TeXitoi/rusty-clock/images/10-power-led-resistor.jpg

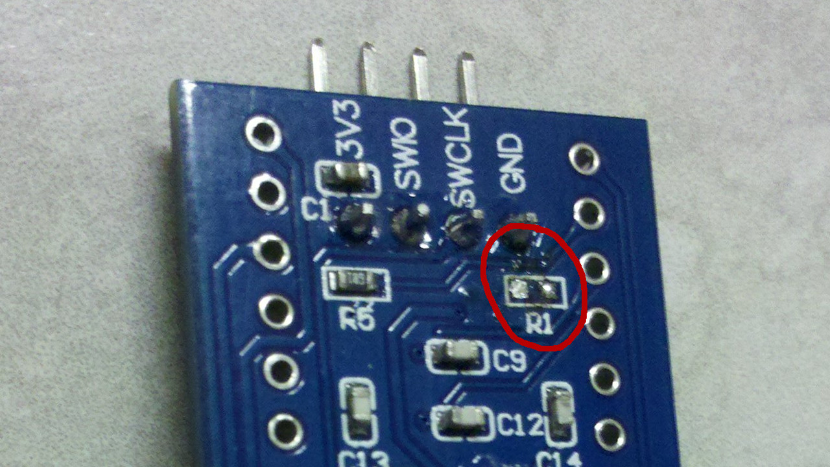
images/10-power-led-resistor.jpg
