TeXitoi/rusty-clock/images/11-blue-pill-headers.jpg

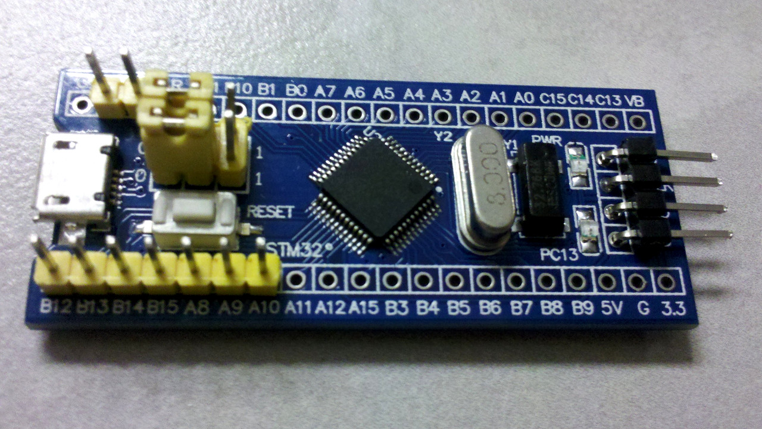
images/11-blue-pill-headers.jpg
