TeXitoi/rusty-clock/images/13-box-and-back.jpg

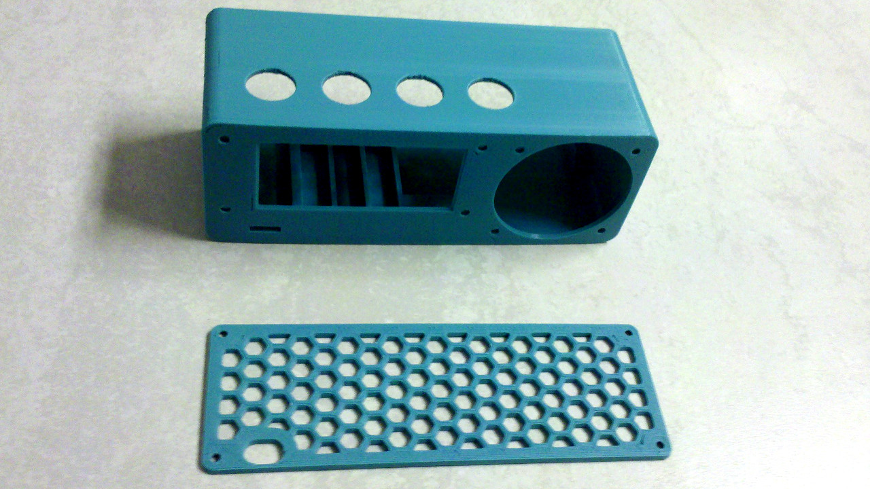
images/13-box-and-back.jpg
