TeXitoi/rusty-clock/images/19-ground-button-wire.jpg

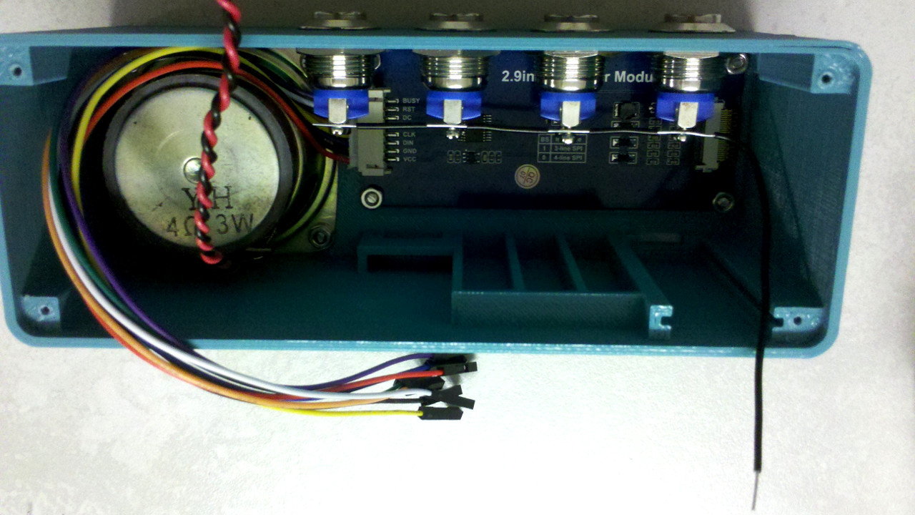
images/19-ground-button-wire.jpg
