TeXitoi/rusty-clock/images/20-wires.jpg

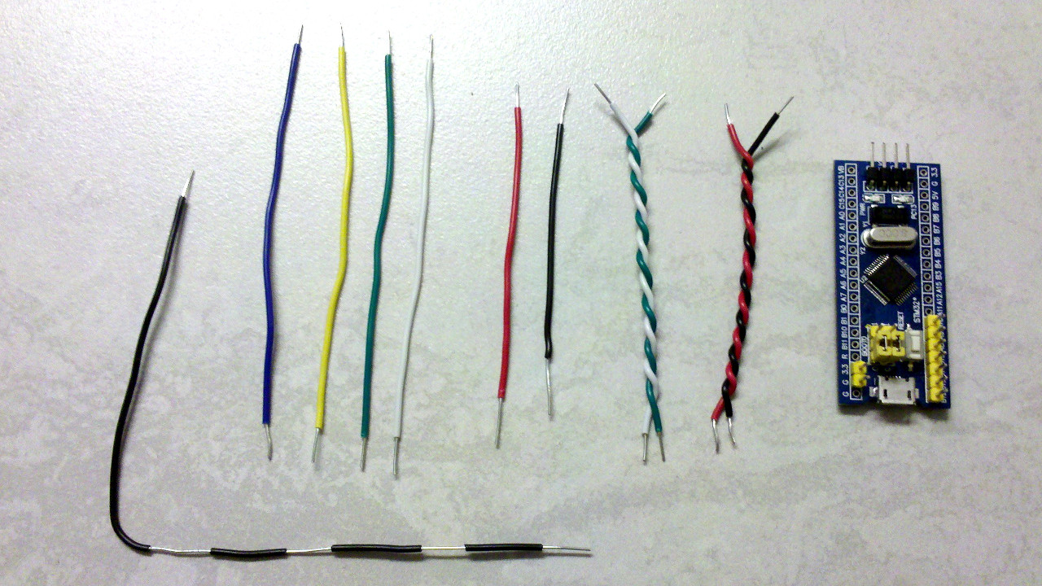
images/20-wires.jpg
