TeXitoi/rusty-clock/cad/box-v2/box-printing.scad

use <box.scad>
include <printing.scad>

box();
