TeXitoi/rusty-clock/images/15-fix-speaker-back.jpg

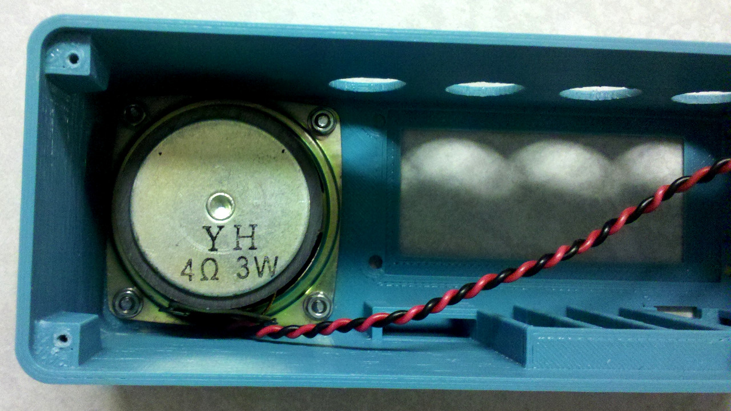
images/15-fix-speaker-back.jpg
