TeXitoi/rusty-clock/images/16-fix-display-front.jpg

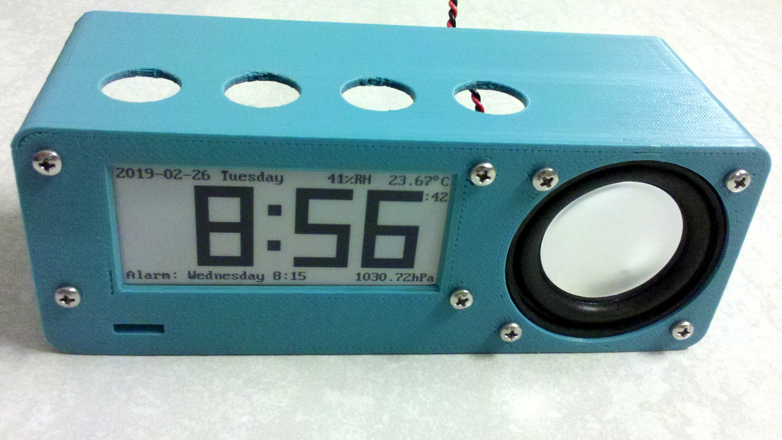
images/16-fix-display-front.jpg
