TeXitoi/rusty-clock/images/18-fix-buttons.jpg

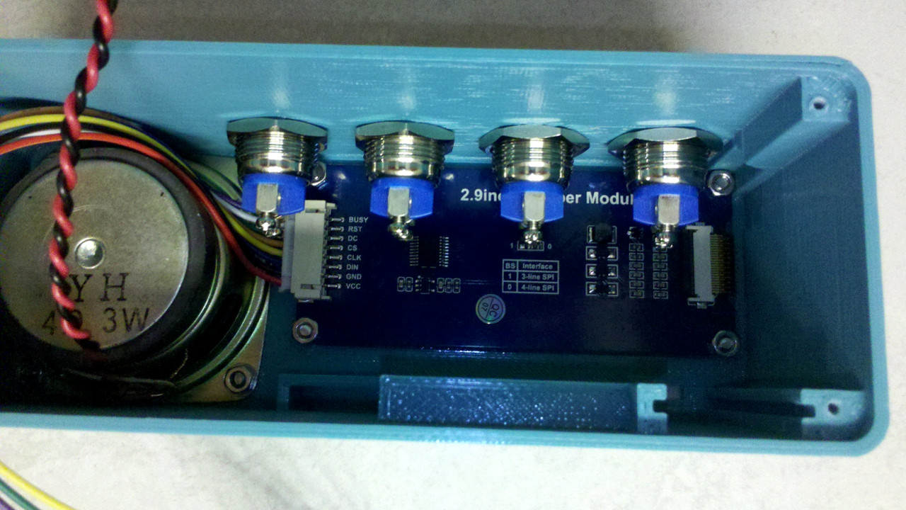
images/18-fix-buttons.jpg
