TeXitoi/rusty-clock/src/ui.rs

use core::convert::TryFrom;
use core::fmt::{self, Write};
use embedded_graphics::coord::Coord;
use embedded_graphics::fonts::{Font6x8, Font8x16};
use embedded_graphics::prelude::*;
use embedded_graphics::primitives::Rect;
use embedded_hal::blocking::i2c::WriteRead;
use heapless::{consts::*, String, Vec};
use il3820::DisplayRibbonLeft;
use rtc::datetime;

pub enum Msg {
    DateTime(datetime::DateTime),
    Environment(::bme280::Measurements<<::I2C as WriteRead>::Error>),
    ButtonMinus,
    ButtonOk,
    ButtonPlus,
}

pub enum Cmd {
    UpdateRtc(datetime::DateTime),
}

#[derive(Clone)]
pub struct Model {
    now: datetime::DateTime,
    /// unit: Pa
    pressure: u32,
    /// unit: c°C
    temperature: i16,
    /// unit: %
    humidity: u8,
    screen: Screen,
}

impl Model {
    pub fn init() -> Self {
        Self {
            now: datetime::DateTime::new(0),
            pressure: 0,
            temperature: 0,
            humidity: 0,
            screen: Screen::Clock,
        }
    }
    pub fn update(&mut self, msg: Msg) -> Vec<Cmd, U4> {
        use self::Screen::*;
        let mut cmds = Vec::new();

        match msg {
            Msg::DateTime(datetime) => self.now = datetime,
            Msg::Environment(measurements) => {
                self.pressure = measurements.pressure as u32;
                self.temperature = (measurements.temperature * 100.) as i16;
                self.humidity = measurements.humidity as u8;
            }
            Msg::ButtonOk => {
                self.screen = match ::core::mem::replace(&mut self.screen, Clock) {
                    Clock => Menu(MenuElt::Clock),
                    Menu(MenuElt::Clock) => Clock,
                    Menu(MenuElt::SetClock) => {
                        let mut dt = self.now.clone();
                        dt.sec = 0;
                        SetClock(EditDateTime::new(dt))
                    }
                    SetClock(mut edit) => if let Some(dt) = edit.ok() {
                        if let Err(_) = cmds.push(Cmd::UpdateRtc(dt)) {
                            panic!("cmds too small");
                        }
                        Clock
                    } else {
                        SetClock(edit)
                    },
                }
            }
            Msg::ButtonPlus => match &mut self.screen {
                Menu(elt) => *elt = elt.next(),
                SetClock(edit) => edit.next(),
                _ => {}
            },
            Msg::ButtonMinus => match &mut self.screen {
                Menu(elt) => *elt = elt.prev(),
                SetClock(edit) => edit.prev(),
                _ => {}
            },
        }
        cmds
    }
    pub fn view(&self) -> DisplayRibbonLeft {
        let mut display = DisplayRibbonLeft::default();

        self.render_header(&mut display);

        use self::Screen::*;
        match &self.screen {
            Clock => self.render_clock(&mut display),
            Menu(elt) => self.render_menu(elt, &mut display),
            SetClock(datetime) => self.render_set_clock(datetime, &mut display),
        }

        display
    }
    fn render_header(&self, display: &mut DisplayRibbonLeft) {
        let mut print = move |s: &str, x, y| {
            display.draw(
                Font6x8::render_str(s)
                    .with_stroke(Some(1u8.into()))
                    .translate(Coord::new(x, y))
                    .into_iter(),
            )
        };
        let mut s: String<U128> = String::new();
        write!(
            s,
            "{:4}-{:02}-{:02} {}",
            self.now.year, self.now.month, self.now.day, self.now.day_of_week,
        ).unwrap();
        print(&s, 4, 4);

        s.clear();
        write!(
            s,
            "{}{}C",
            Centi(self.temperature as i32),
            char::try_from('°' as u32 - 34).unwrap(),
        ).unwrap();
        print(&s, 4, 127 - 10);

        s.clear();
        write!(s, "{}hPa", Centi(self.pressure as i32),).unwrap();
        print(&s, 295 - 4 - 10 * 6, 127 - 10);

        if self.humidity != 0 {
            s.clear();
            write!(s, "{:2}%RH", self.humidity).unwrap();
            print(&s, 296 / 2 - 5 * 3, 127 - 10);
        }
    }
    fn render_clock(&self, display: &mut DisplayRibbonLeft) {
        let margin = 10;
        let digit = 50;
        let space = 12;

        if self.now.hour >= 10 {
            seven_segments(self.now.hour / 10, margin, 18, display);
        }
        seven_segments(self.now.hour % 10, margin + digit + space, 18, display);

        display.draw(
            Rect::new(
                Coord::new(margin + 2 * digit + 2 * space, 18 + 20),
                Coord::new(margin + 2 * digit + 2 * space + 9, 18 + 29),
            ).with_fill(Some(1u8.into()))
            .into_iter(),
        );
        display.draw(
            Rect::new(
                Coord::new(margin + 2 * digit + 2 * space, 18 + 60),
                Coord::new(margin + 2 * digit + 2 * space + 9, 18 + 69),
            ).with_fill(Some(1u8.into()))
            .into_iter(),
        );

        seven_segments(
            self.now.min / 10,
            margin + 2 * digit + 3 * space + 10,
            18,
            display,
        );
        seven_segments(
            self.now.min % 10,
            margin + 3 * digit + 4 * space + 10,
            18,
            display,
        );

        let mut s: String<U4> = String::new();
        write!(s, ":{:02}", self.now.sec).unwrap();
        display.draw(
            Font6x8::render_str(&s)
                .with_stroke(Some(1u8.into()))
                .translate(Coord::new(273, 18))
                .into_iter(),
        );
    }
    fn render_menu(&self, elt: &MenuElt, display: &mut DisplayRibbonLeft) {
        let mut s: String<U128> = String::new();
        write!(s, "Menu: {}", elt).unwrap();
        display.draw(
            Font8x16::render_str(&s)
                .with_stroke(Some(1u8.into()))
                .translate(Coord::new(12, 44))
                .into_iter(),
        );
    }
    fn render_set_clock(&self, datetime: &EditDateTime, display: &mut DisplayRibbonLeft) {
        let mut s: String<U128> = String::new();
        write!(s, "Set clock: {}", datetime).unwrap();
        display.draw(
            Font8x16::render_str(&s)
                .with_stroke(Some(1u8.into()))
                .translate(Coord::new(12, 44))
                .into_iter(),
        );
    }
}

struct Centi(i32);
impl fmt::Display for Centi {
    fn fmt(&self, f: &mut fmt::Formatter) -> fmt::Result {
        write!(f, "{}.{:02}", self.0 / 100, self.0 % 100)
    }
}

#[derive(Clone)]
enum Screen {
    Clock,
    Menu(MenuElt),
    SetClock(EditDateTime),
}
#[derive(Clone)]
enum MenuElt {
    Clock,
    SetClock,
}
impl MenuElt {
    fn next(&self) -> MenuElt {
        use self::MenuElt::*;
        match *self {
            Clock => SetClock,
            SetClock => Clock,
        }
    }
    fn prev(&self) -> MenuElt {
        use self::MenuElt::*;
        match *self {
            Clock => SetClock,
            SetClock => Clock,
        }
    }
}
impl fmt::Display for MenuElt {
    fn fmt(&self, f: &mut fmt::Formatter) -> fmt::Result {
        match self {
            MenuElt::Clock => f.write_str("clock"),
            MenuElt::SetClock => f.write_str("set clock"),
        }
    }
}
#[derive(Clone)]
struct EditDateTime {
    datetime: datetime::DateTime,
    state: EditDateTimeState,
}
#[derive(Clone)]
enum EditDateTimeState {
    Year,
    Month,
    Day,
    Hour,
    Min,
}
impl EditDateTime {
    fn new(datetime: datetime::DateTime) -> Self {
        Self {
            datetime,
            state: EditDateTimeState::Year,
        }
    }
    fn next(&mut self) {
        use self::EditDateTimeState::*;
        match self.state {
            Year => {
                self.datetime.year += 1;
                if self.datetime.year > 2105 {
                    self.datetime.year = 1970;
                }
            }
            Month => self.datetime.month = self.datetime.month % 12 + 1,
            Day => self.datetime.day = self.datetime.day % 31 + 1,
            Hour => self.datetime.hour = (self.datetime.hour + 1) % 24,
            Min => self.datetime.min = (self.datetime.min + 1) % 60,
        }
    }
    fn prev(&mut self) {
        use self::EditDateTimeState::*;
        match self.state {
            Year => {
                self.datetime.year -= 1;
                if self.datetime.year < 1970 {
                    self.datetime.year = 2105;
                }
            }
            Month => self.datetime.month = (self.datetime.month + 12 - 2) % 12 + 1,
            Day => self.datetime.day = (self.datetime.day + 31 - 2) % 31 + 1,
            Hour => self.datetime.hour = (self.datetime.hour + 24 - 1) % 24,
            Min => self.datetime.min = (self.datetime.min + 60 - 1) % 60,
        }
    }
    fn ok(&mut self) -> Option<datetime::DateTime> {
        use self::EditDateTimeState::*;
        match self.state {
            Year => self.state = Month,
            Month => self.state = Day,
            Day => self.state = Hour,
            Hour => self.state = Min,
            Min => return Some(self.datetime.clone()),
        }
        None
    }
}
impl fmt::Display for EditDateTime {
    fn fmt(&self, f: &mut fmt::Formatter) -> fmt::Result {
        use self::EditDateTimeState::*;
        match self.state {
            Year => write!(f, "year: {}", self.datetime.year),
            Month => write!(f, "month: {}", self.datetime.month),
            Day => write!(f, "day: {}", self.datetime.day),
            Hour => write!(f, "hour: {}", self.datetime.hour),
            Min => write!(f, "min: {}", self.datetime.min),
        }
    }
}

fn seven_segments(c: u8, x: i32, y: i32, display: &mut DisplayRibbonLeft) {
    fn s(s: u8) -> u8 {
        1 << s
    }
    let segments = match c {
        0 => s(0) | s(1) | s(2) | s(4) | s(5) | s(6),
        1 => s(2) | s(5),
        2 => s(0) | s(2) | s(3) | s(4) | s(6),
        3 => s(0) | s(2) | s(3) | s(5) | s(6),
        4 => s(1) | s(2) | s(3) | s(5),
        5 => s(0) | s(1) | s(3) | s(5) | s(6),
        6 => s(0) | s(1) | s(3) | s(4) | s(5) | s(6),
        7 => s(0) | s(2) | s(5),
        8 => s(0) | s(1) | s(2) | s(3) | s(4) | s(5) | s(6),
        9 => s(0) | s(1) | s(2) | s(3) | s(5) | s(6),
        _ => 0,
    };
    let w = 50;
    let h = 90;
    let t = 10;
    let h2 = (h - 3 * t) / 2 + t;
    if segments & 1 != 0 {
        display.draw(
            Rect::new(Coord::new(0, 0), Coord::new(w - 1, t - 1))
                .with_fill(Some(1u8.into()))
                .translate(Coord::new(x, y))
                .into_iter(),
        );
    }
    if segments & (1 << 1) != 0 {
        display.draw(
            Rect::new(Coord::new(0, 0), Coord::new(t - 1, h2 + t - 1))
                .with_fill(Some(1u8.into()))
                .translate(Coord::new(x, y))
                .into_iter(),
        );
    }
    if segments & (1 << 2) != 0 {
        display.draw(
            Rect::new(Coord::new(w - t, 0), Coord::new(w - 1, h2 + t - 1))
                .with_fill(Some(1u8.into()))
                .translate(Coord::new(x, y))
                .into_iter(),
        );
    }
    if segments & (1 << 3) != 0 {
        display.draw(
            Rect::new(Coord::new(t, h2), Coord::new(w - t - 1, h2 + t - 1))
                .with_fill(Some(1u8.into()))
                .translate(Coord::new(x, y))
                .into_iter(),
        );
    }
    if segments & (1 << 4) != 0 {
        display.draw(
            Rect::new(Coord::new(0, h2), Coord::new(t - 1, h - 1))
                .with_fill(Some(1u8.into()))
                .translate(Coord::new(x, y))
                .into_iter(),
        );
    }
    if segments & (1 << 5) != 0 {
        display.draw(
            Rect::new(Coord::new(w - t, h2), Coord::new(w - 1, h - 1))
                .with_fill(Some(1u8.into()))
                .translate(Coord::new(x, y))
                .into_iter(),
        );
    }
    if segments & (1 << 6) != 0 {
        display.draw(
            Rect::new(Coord::new(0, h - t), Coord::new(w - 1, h - 1))
                .with_fill(Some(1u8.into()))
                .translate(Coord::new(x, y))
                .into_iter(),
        );
    }
}
